hackmeopen/Vectr/Vectr_Firmware/quantization_tables.c

#include "system_config.h"
#include "quantization_tables.h"

const uint32_t u32QuantizedSpeedTable[15] = {
    ZERO_SPEED_VALUE/8,
    ZERO_SPEED_VALUE/7,
    ZERO_SPEED_VALUE/6,
    ZERO_SPEED_VALUE/5,
    ZERO_SPEED_VALUE/4,
    ZERO_SPEED_VALUE/3,
    ZERO_SPEED_VALUE/2,
    ZERO_SPEED_VALUE,
    ZERO_SPEED_VALUE*2,
    ZERO_SPEED_VALUE*3,
    ZERO_SPEED_VALUE*4,
    ZERO_SPEED_VALUE*5,
    ZERO_SPEED_VALUE*6,
    ZERO_SPEED_VALUE*7,
    ZERO_SPEED_VALUE*8
};

const uint32_t u32LogSpeedTable[	1024]={
	1919992	,
	1733326	,
	1624134	,
	1546660	,
	1486567	,
	1437468	,
	1395955	,
	1359994	,
	1328275	,
	1299901	,
	1274234	,
	1250802	,
	1229246	,
	1209289	,
	1190709	,
	1173328	,
	1157002	,
	1141609	,
	1127049	,
	1113235	,
	1100096	,
	1087568	,
	1075597	,
	1064136	,
	1053142	,
	1042580	,
	1032417	,
	1022623	,
	1013173	,
	1004043	,
	995213	,
	986663	,
	978376	,
	970336	,
	962530	,
	954943	,
	947565	,
	940383	,
	933388	,
	926570	,
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


const uint16_t u16LogTable[	1024]={
	0	,
	141	,
	280	,
	418	,
	555	,
	691	,
	825	,
	958	,
	1089	,
	1220	,
	2462	,
	3604	,
	4661	,
	5645	,
	6564	,
	7428	,
	8241	,
	9011	,
	9741	,
	10435	,
	11096	,
	11728	,
	12333	,
	12913	,
	13471	,
	14007	,
	14524	,
	15022	,
	15504	,
	15969	,
	16420	,
	16857	,
	17281	,
	17693	,
	18092	,
	18481	,
	18860	,
	19228	,
	19588	,
	19938	,
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




const uint16_t u16ChromaticScale[LENGTH_OF_CHROMATIC_SCALE] = {
0	,	//	0
546	,	//	1
1092	,	//	2
1638	,	//	3
2185	,	//	4
2731	,	//	5
3277	,	//	6
3823	,	//	7
4369	,	//	8
4915	,	//	9
5461	,	//	10
6007	,	//	11
6554	,	//	12
7100	,	//	13
7646	,	//	14
8192	,	//	15
8738	,	//	16
9284	,	//	17
9830	,	//	18
10376	,	//	19
10923	,	//	20
11469	,	//	21
12015	,	//	22
12561	,	//	23
13107	,	//	24
13653	,	//	25
14199	,	//	26
14745	,	//	27
15292	,	//	28
15838	,	//	29
16384	,	//	30
16930	,	//	31
17476	,	//	32
18022	,	//	33
18568	,	//	34
19114	,	//	35
19661	,	//	36
20207	,	//	37
20753	,	//	38
21299	,	//	39
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
};

const uint16_t u16MinorScale[71]= {
0	,
1092	,
1638	,
2731	,
3823	,
4369	,
5461	,
6554	,
7646	,
8192	,
9284	,
10376	,
10923	,
12015	,
13107	,
14199	,
14745	,
15838	,
16930	,
17476	,
18568	,
19661	,
20753	,
21299	,
22391	,
23483	,
24030	,
25122	,
26214	,
27306	,
27852	,
28945	,
30037	,
30583	,
31675	,
32768	,
33860	,
34406	,
35498	,
36590	,
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
};

const uint16_t u16PentatonicScale[51]={
0	,
1092	,
2185	,
3823	,
4915	,
6554	,
7646	,
8738	,
10376	,
11469	,
13107	,
14199	,
15292	,
16930	,
18022	,
19661	,
20753	,
21845	,
23483	,
24576	,
26214	,
27306	,
28399	,
30037	,
31129	,
32768	,
33860	,
34952	,
36590	,
37683	,
39321	,
40413	,
41506	,
43144	,
44236	,
45875	,
46967	,
48059	,
49697	,
50790	,
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
};

const uint16_t u16OctaveScale[11]={
0	,
6554	,
13107	,
19661	,
26214	,
32768	,
39321	,
45875	,
52428	,
58982	,
65535	
};
